matrixneo99/docs/v2/assets/AWTRIX_Node.jpg

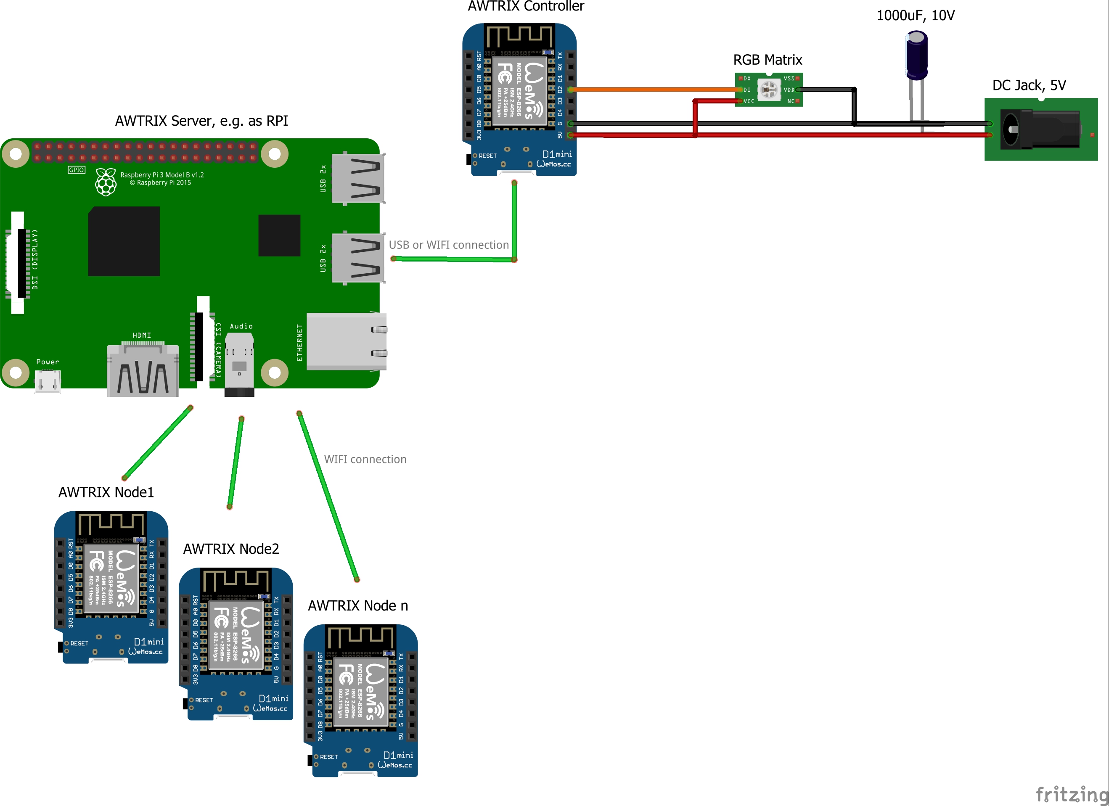
v2/assets/AWTRIX_Node.jpg
