matrixneo99/docs/v2/assets/image_3.png

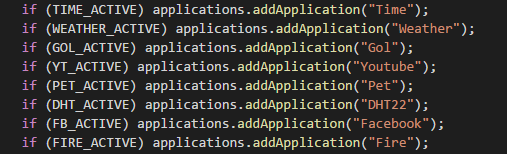
v2/assets/image_3.png
