matrixneo99/docs/v2/assets/minecraft.png

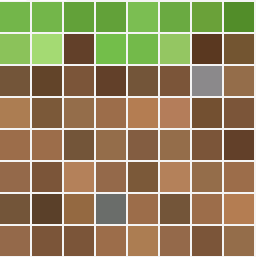
v2/assets/minecraft.png
