matrixneo99/docs/v2/assets/OTA_update_AWTRIXController.jpg

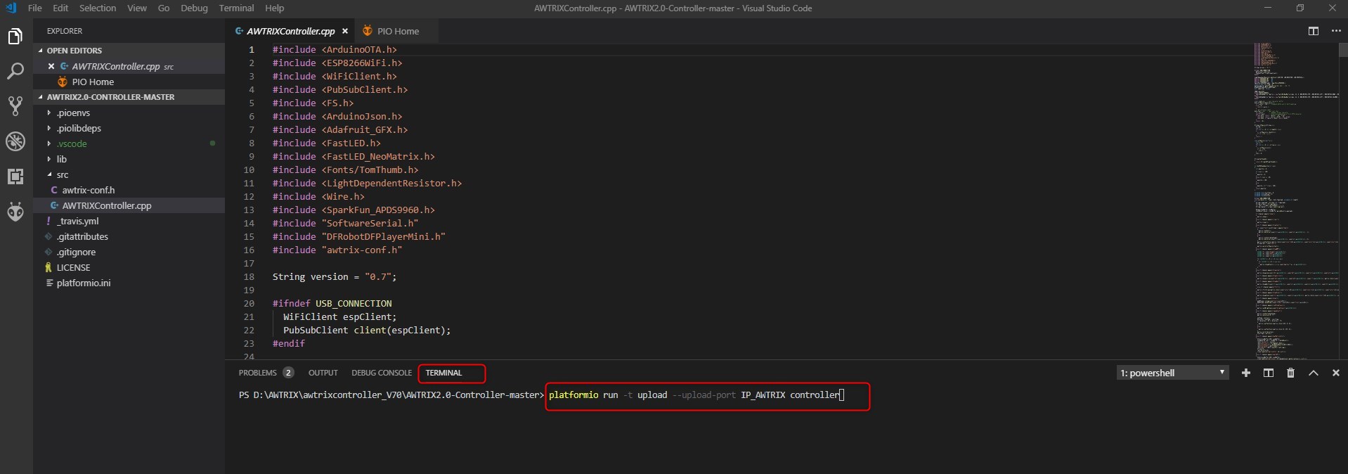
v2/assets/OTA_update_AWTRIXController.jpg
