matrixneo99/docs/v2/assets/plattformio_update.jpg

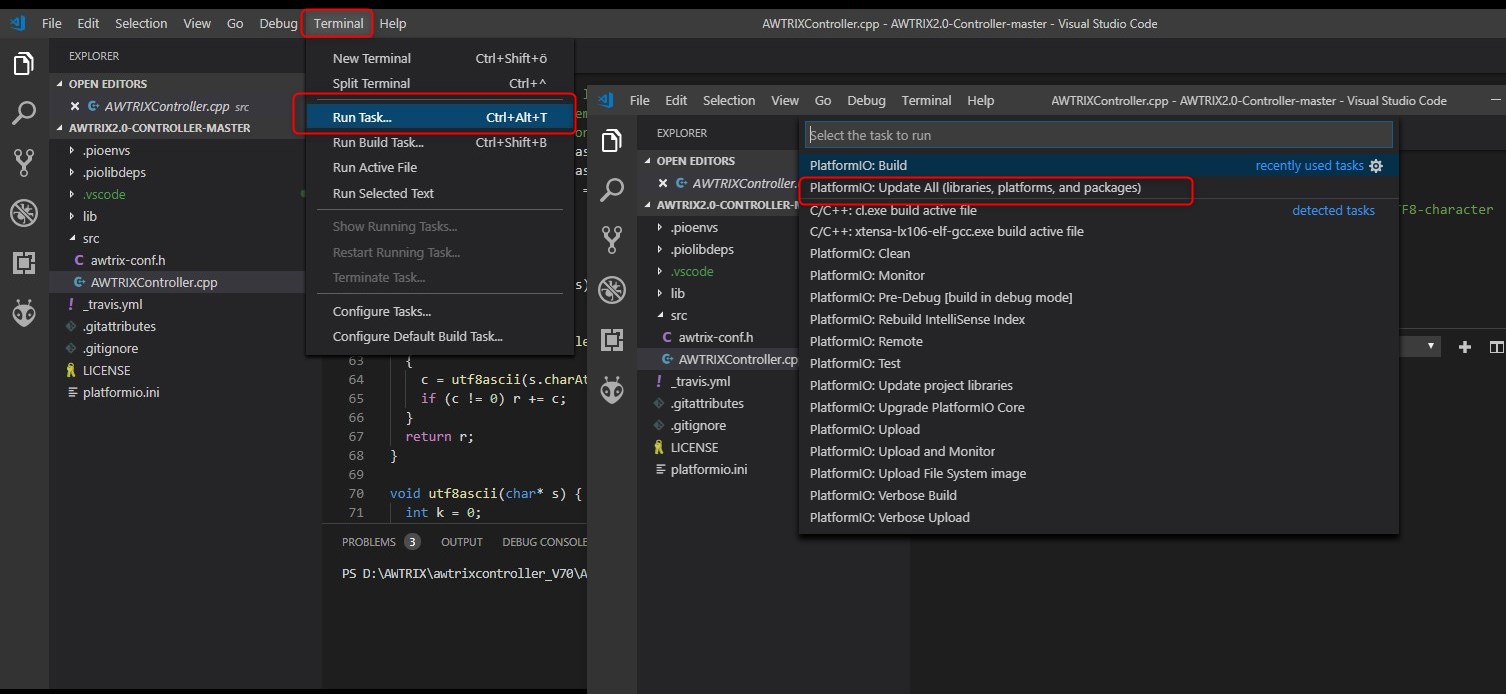
v2/assets/plattformio_update.jpg
