matrixneo99/docs/v2/assets/tronaldump.png

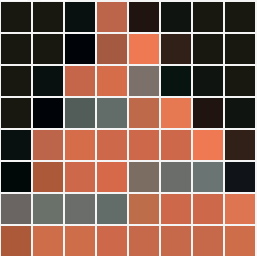
v2/assets/tronaldump.png
